parallellogic-/SuperconAddOn2024/src/sao2024/application.h

#include "api.h"

void run_application(void);
u8 set_frame_rainbow(bool is_circular);
u8 set_sparkles(bool is_fireworks);
u8 show_screensaver(u8 screensaver_index);
void set_element_hue(u8 led_index,u8 color_index);
